retro-esp32/RetroESP32-Design-Files/Assets/Watermark/001.png

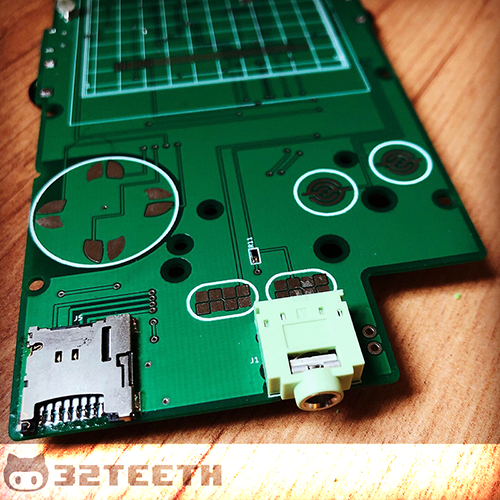
Assets/Watermark/001.png
