retro-esp32/RetroESP32-Design-Files/Assets/Watermark/002.png

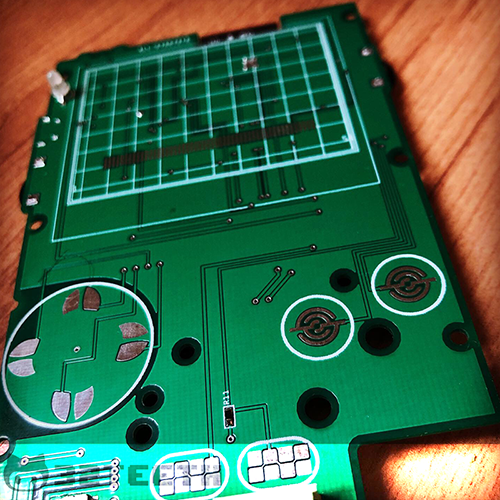
Assets/Watermark/002.png
