retro-esp32/RetroESP32-Design-Files/Assets/Watermark/003.png

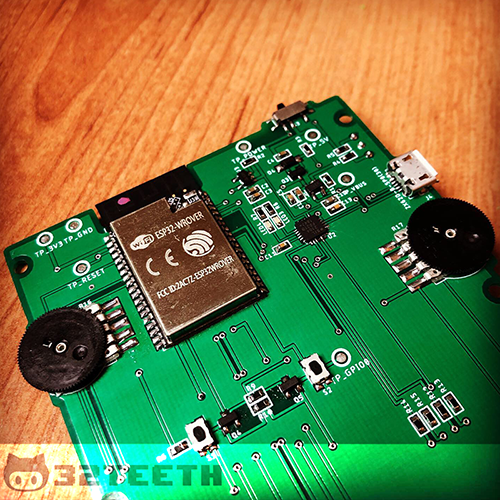
Assets/Watermark/003.png
