retro-esp32/RetroESP32-Design-Files/Assets/Watermark/004.png

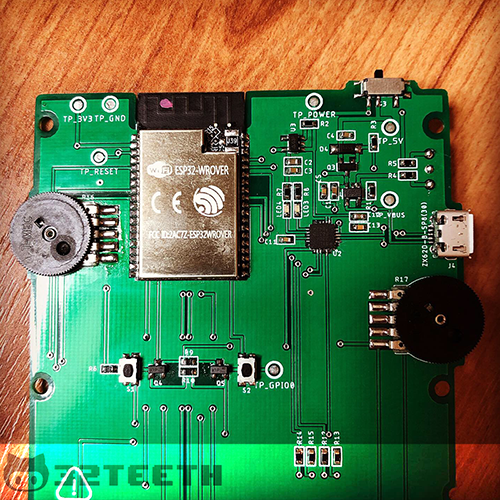
Assets/Watermark/004.png
