retro-esp32/RetroESP32-Design-Files/Assets/Watermark/005.png

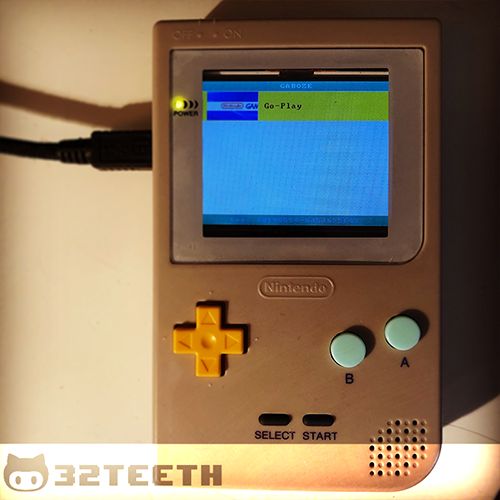
Assets/Watermark/005.png
