retro-esp32/RetroESP32-Design-Files/Assets/Watermark/006.png

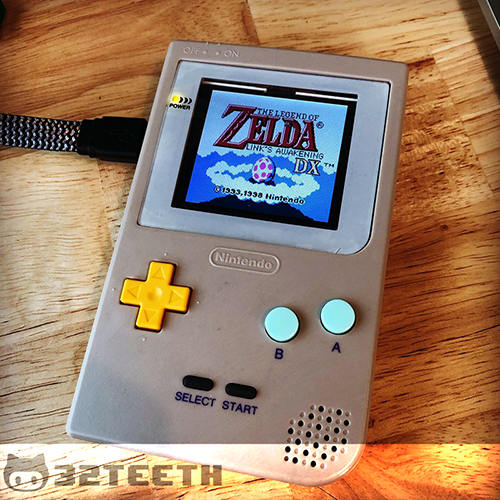
Assets/Watermark/006.png
