retro-esp32/RetroESP32-Design-Files/Assets/Watermark/007.png

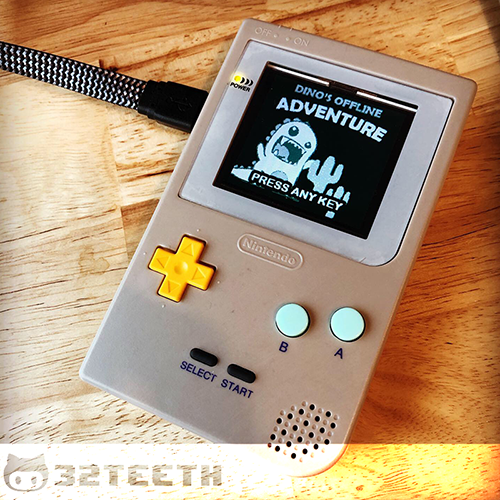
Assets/Watermark/007.png
