retro-esp32/RetroESP32-Design-Files/Assets/Watermark/008.png

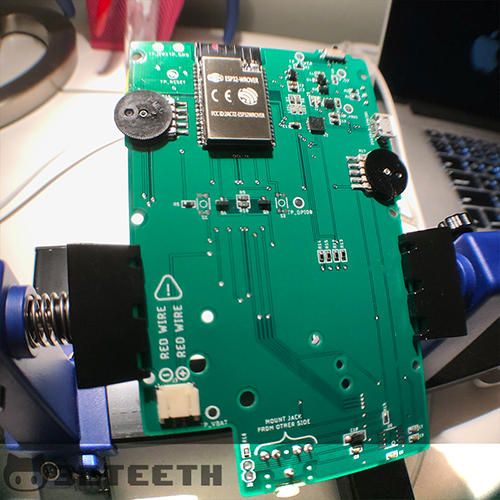
Assets/Watermark/008.png
