retro-esp32/RetroESP32-Design-Files/Assets/Watermark/009.png

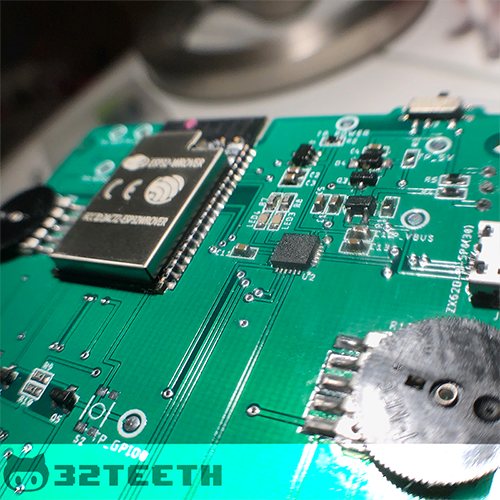
Assets/Watermark/009.png
