retro-esp32/RetroESP32-Design-Files/Assets/Watermark/010.png

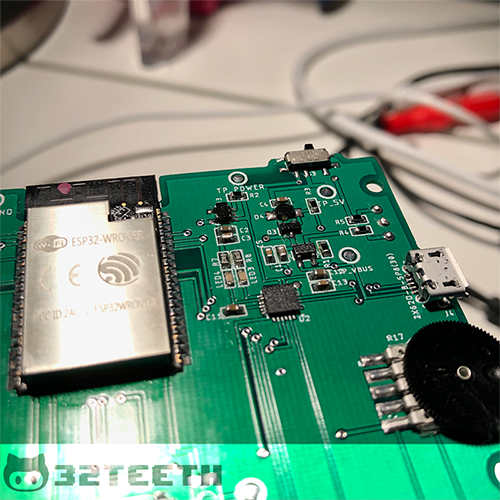
Assets/Watermark/010.png
